embarcados-virtus-cc/optic-power-meter-portable/sfp_8472/a0h.c

/**
 * @file sfp_8472_a0h.c
 * @brief Biblioteca de parsing SFF-8472 – Página A0h (Base ID)
 *
 * @author Alexandre Junior
 * @author Carlos Elias
 * @author Melquisedeque Leite
 * @author Miguel Ryan
 * @author Nicholas Gomes
 * @author Pablo Daniel
 * @author Pedro Lucena
 * @author Pedro Wilson
 *
 * @details
 *  Implementa a leitura e interpretação dos campos da EEPROM A0h
 *  de módulos SFP/SFP+, conforme a especificação SFF-8472.
 */

#include "a0h.h"
#include "defs.h"
#include <stdio.h>
#include <string.h>
#include <stdint.h>

/* ============================================
 * Byte 0 — Identifier
 * ============================================ */
void sfp_parse_a0_base_identifier(const uint8_t *a0_base_data, sfp_a0h_base_t *a0)
{
    if (!a0_base_data || !a0)
        return;

    a0->identifier = (sfp_identifier_t)a0_base_data[A0_IDENTIFIER];
}

/* ============================================
 * Função Getter
 * ============================================ */
sfp_identifier_t sfp_a0_get_identifier(const sfp_a0h_base_t *a0)
{
    if (!a0)
        return SFP_ID_UNKNOWN;

    return a0->identifier;
}

/* ============================================
 * Byte 1 — Extended Identifier
 * ============================================ */
void sfp_parse_a0_base_ext_identifier(const uint8_t *a0_base_data, sfp_a0h_base_t *a0)
{
    if (!a0_base_data || !a0)
        return;

    a0->ext_identifier = a0_base_data[A0_EXT_IDENTIFIER];
}

/* ============================================
 * Função Getter
 * ============================================ */
uint8_t sfp_a0_get_ext_identifier(const sfp_a0h_base_t *a0)
{
    if (!a0)
        return 0x00;

    return a0->ext_identifier;
}

bool sfp_validate_ext_identifier(const sfp_a0h_base_t *a0)
{
    if (!a0)
        return false;

    return (a0->ext_identifier == SFP_EXT_IDENTIFIER_EXPECTED);
}

/* ============================================
 * Byte 2 — Connector
 * ============================================ */
void sfp_parse_a0_base_connector(const uint8_t *a0_base_data, sfp_a0h_base_t *a0)
{
    if (!a0_base_data || !a0)
        return;

    uint8_t connector_raw = a0_base_data[A0_CONNECTOR];
    a0->connector = (sfp_connector_type_t)connector_raw;
}

/* ============================================
 * Função Getter
 * ============================================ */
sfp_connector_type_t sfp_a0_get_connector(const sfp_a0h_base_t *a0)
{
    if (!a0)
        return SFP_CONNECTOR_UNKNOWN;

    return a0->connector;
}

/* ============================================
 * Função de Exposição
 * ============================================ */
const char *sfp_connector_to_string(sfp_connector_type_t connector)
{
    switch (connector) {
        case SFP_CONNECTOR_SC:
            return "SC";
        case SFP_CONNECTOR_FC_STYLE_1:
            return "Fibre Channel Style 1";
        case SFP_CONNECTOR_FC_STYLE_2:
            return "Fibre Channel Style 2";
        case SFP_CONNECTOR_BNC_TNC:
            return "BNC/TNC";
        case SFP_CONNECTOR_FC_COAX:
            return "Fibre Channel Coax";
        case SFP_CONNECTOR_FIBER_JACK:
            return "Fiber Jack";
        case SFP_CONNECTOR_LC:
            return "LC";
        case SFP_CONNECTOR_MT_RJ:
            return "MT-RJ";
        case SFP_CONNECTOR_MU:
            return "MU";
        case SFP_CONNECTOR_SG:
            return "SG";
        case SFP_CONNECTOR_OPTICAL_PIGTAIL:
            return "Optical Pigtail";
        case SFP_CONNECTOR_MPO_1X12:
            return "MPO 1x12";
        case SFP_CONNECTOR_MPO_2X16:
            return "MPO 2x16";
        case SFP_CONNECTOR_HSSDC_II:
            return "HSSDC II";
        case SFP_CONNECTOR_COPPER_PIGTAIL:
            return "Copper Pigtail";
        case SFP_CONNECTOR_RJ45:
            return "RJ45";
        case SFP_CONNECTOR_NO_SEPARABLE:
            return "No Separable Connector";
        default:
            return "Unknown Connector";
    }
}

/* ============================================
 * Bytes 3-10 — Compliance Codes
 * ============================================ */
void sfp_parse_a0_base_compliance(const uint8_t *a0_base_data, sfp_compliance_codes_t *cc)
{
    if (!a0_base_data || !cc)
        return;

    cc->byte3  = a0_base_data[A0_TRANSCEIVER + 0];
    cc->byte4  = a0_base_data[A0_TRANSCEIVER + 1];
    cc->byte5  = a0_base_data[A0_TRANSCEIVER + 2];
    cc->byte6  = a0_base_data[A0_TRANSCEIVER + 3];
    cc->byte7  = a0_base_data[A0_TRANSCEIVER + 4];
    cc->byte8  = a0_base_data[A0_TRANSCEIVER + 5];
    cc->byte9  = a0_base_data[A0_TRANSCEIVER + 6];
    cc->byte10 = a0_base_data[A0_TRANSCEIVER + 7];
}

/* ============================================
 * Decode do Byte 3
 * ============================================ */
static void decode_byte3(const sfp_compliance_codes_t *cc, sfp_compliance_decoded_t *out)
{
    uint8_t b = cc->byte3;
    out->eth_10g_base_er               = (b & (1 << 7)) != 0;
    out->eth_10g_base_lrm              = (b & (1 << 6)) != 0;
    out->eth_10g_base_lr               = (b & (1 << 5)) != 0;
    out->eth_10g_base_sr               = (b & (1 << 4)) != 0;
    out->infiniband_1x_sx              = (b & (1 << 3)) != 0;
    out->infiniband_1x_lx              = (b & (1 << 2)) != 0;
    out->infiniband_1x_copper_active   = (b & (1 << 1)) != 0;
    out->infiniband_1x_copper_passive  = (b & (1 << 0)) != 0;
}

/* ============================================
 * Decode do Byte 4
 * ============================================ */
static void decode_byte4(const sfp_compliance_codes_t *cc, sfp_compliance_decoded_t *out)
{
    uint8_t b = cc->byte4;
    out->escon_mmf  = (b & (1 << 7)) != 0;
    out->escon_smf  = (b & (1 << 6)) != 0;
    out->oc_192_sr  = (b & (1 << 5)) != 0;
    out->sonet_rs_1 = (b & (1 << 4)) != 0;
    out->sonet_rs_2 = (b & (1 << 3)) != 0;
    out->oc_48_lr   = (b & (1 << 2)) != 0;
    out->oc_48_ir   = (b & (1 << 1)) != 0;
    out->oc_48_sr   = (b & (1 << 0)) != 0;
}

/* ============================================
 * Decode do Byte 5
 * ============================================ */
static void decode_byte5(const sfp_compliance_codes_t *cc, sfp_compliance_decoded_t *out)
{
    uint8_t b = cc->byte5;
    out->oc_12_sm_lr = (b & (1 << 6)) != 0;
    out->oc_12_sm_ir = (b & (1 << 5)) != 0;
    out->oc_12_sr    = (b & (1 << 4)) != 0;
    out->oc_3_sm_lr  = (b & (1 << 2)) != 0;
    out->oc_3_sm_ir  = (b & (1 << 1)) != 0;
    out->oc_3_sr     = (b & (1 << 0)) != 0;
}

/* ============================================
 * Decode do Byte 6
 * ============================================ */
static void decode_byte6(const sfp_compliance_codes_t *cc, sfp_compliance_decoded_t *out)
{
    uint8_t b = cc->byte6;
    out->eth_base_px      = (b & (1 << 7)) != 0;
    out->eth_base_bx_10   = (b & (1 << 6)) != 0;
    out->eth_100_base_fx  = (b & (1 << 5)) != 0;
    out->eth_100_base_lx  = (b & (1 << 4)) != 0;
    out->eth_1000_base_t  = (b & (1 << 3)) != 0;
    out->eth_1000_base_cx = (b & (1 << 2)) != 0;
    out->eth_1000_base_lx = (b & (1 << 1)) != 0;
    out->eth_1000_base_sx = (b & (1 << 0)) != 0;
}

/* ============================================
 * Decode do Byte 7
 * ============================================ */
static void decode_byte7(const sfp_compliance_codes_t *cc, sfp_compliance_decoded_t *out)
{
    uint8_t b = cc->byte7;
    out->fc_very_long_distance      = (b & (1 << 7)) != 0;
    out->fc_short_distance          = (b & (1 << 6)) != 0;
    out->fc_intermediate_distance   = (b & (1 << 5)) != 0;
    out->fc_long_distance           = (b & (1 << 4)) != 0;
    out->fc_medium_distance         = (b & (1 << 3)) != 0;
    out->shortwave_laser_sa         = (b & (1 << 2)) != 0;
    out->longwave_laser_lc          = (b & (1 << 1)) != 0;
    out->electrical_inter_enclosure = (b & (1 << 0)) != 0;
}

/* ============================================
 * Decode do Byte 8
 * ============================================ */
static void decode_byte8(const sfp_compliance_codes_t *cc, sfp_compliance_decoded_t *out)
{
    uint8_t b = cc->byte8;
    out->electrical_intra_enclosure = (b & (1 << 7)) != 0;
    out->shortwave_laser_sn         = (b & (1 << 6)) != 0;
    out->shortwave_laser_sl        = (b & (1 << 5)) != 0;
    out->longwave_laser_ll          = (b & (1 << 4)) != 0;
    out->active_cable               = (b & (1 << 3)) != 0;
    out->passive_cable              = (b & (1 << 2)) != 0;
}

/* ============================================
 * Decode do Byte 9
 * ============================================ */
static void decode_byte9(const sfp_compliance_codes_t *cc, sfp_compliance_decoded_t *out)
{
    uint8_t b = cc->byte9;
    out->twin_axial_pair = (b & (1 << 7)) != 0;
    out->twisted_pair    = (b & (1 << 6)) != 0;
    out->miniature_coax  = (b & (1 << 5)) != 0;
    out->video_coax      = (b & (1 << 4)) != 0;
    out->multimode_m6    = (b & (1 << 3)) != 0;
    out->multimode_m5    = (b & (1 << 2)) != 0;
    out->single_mode     = (b & (1 << 0)) != 0;
}

/* ============================================
 * Decode do Byte 10
 * ============================================ */
static void decode_byte10(const sfp_compliance_codes_t *cc, sfp_compliance_decoded_t *out)
{
    uint8_t b = cc->byte10;
    out->cs_1200_mbps = (b & (1 << 7)) != 0;
    out->cs_800_mbps  = (b & (1 << 6)) != 0;
    out->cs_1600_mbps = (b & (1 << 5)) != 0;
    out->cs_400_mbps  = (b & (1 << 4)) != 0;
    out->cs_3200_mbps = (b & (1 << 3)) != 0;
    out->cs_200_mbps  = (b & (1 << 2)) != 0;
    out->see_byte_62  = (b & (1 << 1)) != 0;
    out->cs_100_mbps  = (b & (1 << 0)) != 0;
}

/* ============================================
 * Função principal para decodificação de todos os bytes
 * ============================================ */
void sfp_a0_decode_compliance(const sfp_compliance_codes_t *cc, sfp_compliance_decoded_t *out)
{
    if (!cc || !out)
        return;

    memset(out, 0, sizeof(*out));
    decode_byte3(cc, out);
    decode_byte4(cc, out);
    decode_byte5(cc, out);
    decode_byte6(cc, out);
    decode_byte7(cc, out);
    decode_byte8(cc, out);
    decode_byte9(cc, out);
    decode_byte10(cc, out);
}

/* ============================================
 * Função de Exposição
 * ============================================ */
void sfp_a0_print_compliance(const sfp_compliance_decoded_t *c)
{
    if (!c) return;

    /* ==============================
     * Byte 3 — Ethernet / InfiniBand
     * ============================== */
    printf("\n[Byte 3] Ethernet / InfiniBand:\n");

    if (c->eth_10g_base_er)  printf("  - 10GBASE-ER\n");
    if (c->eth_10g_base_lrm) printf("  - 10GBASE-LRM\n");
    if (c->eth_10g_base_lr)  printf("  - 10GBASE-LR\n");
    if (c->eth_10g_base_sr)  printf("  - 10GBASE-SR\n");

    if (c->infiniband_1x_sx)             printf("  - InfiniBand 1X SX\n");
    if (c->infiniband_1x_lx)             printf("  - InfiniBand 1X LX\n");
    if (c->infiniband_1x_copper_active)  printf("  - InfiniBand 1X Copper Active\n");
    if (c->infiniband_1x_copper_passive) printf("  - InfiniBand 1X Copper Passive\n");

    /* ======================
     * Byte 4 — ESCON / SONET
     * ====================== */
    printf("\n[Byte 4] ESCON / SONET:\n");

    if (c->escon_mmf)   printf("  - ESCON MMF\n");
    if (c->escon_smf)   printf("  - ESCON SMF\n");
    if (c->oc_192_sr)   printf("  - OC-192 SR\n");
    if (c->sonet_rs_1)  printf("  - SONET RS-1\n");
    if (c->sonet_rs_2)  printf("  - SONET RS-2\n");
    if (c->oc_48_lr)    printf("  - OC-48 LR\n");
    if (c->oc_48_ir)    printf("  - OC-48 IR\n");
    if (c->oc_48_sr)    printf("  - OC-48 SR\n");

    /* ======================
     * Byte 5 — SONET
     * ====================== */
    printf("\n[Byte 5] SONET:\n");

    if (c->oc_12_sm_lr) printf("  - OC-12 SM LR\n");
    if (c->oc_12_sm_ir) printf("  - OC-12 SM IR\n");
    if (c->oc_12_sr)    printf("  - OC-12 SR\n");
    if (c->oc_3_sm_lr)  printf("  - OC-3 SM LR\n");
    if (c->oc_3_sm_ir)  printf("  - OC-3 SM IR\n");
    if (c->oc_3_sr)     printf("  - OC-3 SR\n");

    /* ======================
     * Byte 6 — Ethernet
     * ====================== */
    printf("\n[Byte 6] Ethernet:\n");

    if (c->eth_base_px)      printf("  - BASE-PX\n");
    if (c->eth_base_bx_10)   printf("  - BASE-BX10\n");
    if (c->eth_100_base_fx)  printf("  - 100BASE-FX\n");
    if (c->eth_100_base_lx)  printf("  - 100BASE-LX\n");
    if (c->eth_1000_base_t)  printf("  - 1000BASE-T\n");
    if (c->eth_1000_base_cx) printf("  - 1000BASE-CX\n");
    if (c->eth_1000_base_lx) printf("  - 1000BASE-LX\n");
    if (c->eth_1000_base_sx) printf("  - 1000BASE-SX\n");

    /* ====================================
     * Byte 7 — FC Link Length & Technology
     * ==================================== */
    printf("\n[Byte 7] Fibre Channel — Link Length / Technology:\n");

    if (c->fc_very_long_distance)      printf("  - Very Long Distance\n");
    if (c->fc_short_distance)          printf("  - Short Distance\n");
    if (c->fc_intermediate_distance)   printf("  - Intermediate Distance\n");
    if (c->fc_long_distance)           printf("  - Long Distance\n");
    if (c->fc_medium_distance)         printf("  - Medium Distance\n");
    if (c->shortwave_laser_sa)          printf("  - Shortwave Laser (SA)\n");
    if (c->longwave_laser_lc)           printf("  - Longwave Laser (LC)\n");
    if (c->electrical_inter_enclosure)  printf("  - Electrical Inter-Enclosure\n");

    /* ==============================================
     * Byte 8 — FC & SFP+ Cable Technology
     * ============================================== */
    printf("\n[Byte 8] Fibre Channel / Cable Technology:\n");

    if (c->electrical_intra_enclosure) printf("  - Electrical Intra-Enclosure\n");
    if (c->shortwave_laser_sn)         printf("  - Shortwave Laser (SN)\n");
    if (c->shortwave_laser_sl)         printf("  - Shortwave Laser (SL)\n");
    if (c->longwave_laser_ll)          printf("  - Longwave Laser (LL)\n");
    if (c->active_cable)               printf("  - Active SFP+ Cable\n");
    if (c->passive_cable)              printf("  - Passive SFP+ Cable\n");

    /* ==============================
     * Byte 9 — FC Transmission Media
     * ============================== */
    printf("\n[Byte 9] Fibre Channel — Transmission Media:\n");

    if (c->twin_axial_pair) printf("  - Twin Axial Pair\n");
    if (c->twisted_pair)    printf("  - Twisted Pair\n");
    if (c->miniature_coax)  printf("  - Miniature Coax\n");
    if (c->video_coax)      printf("  - Video Coax\n");
    if (c->multimode_m6)    printf("  - Multimode 62.5 µm\n");
    if (c->multimode_m5)    printf("  - Multimode 50 µm\n");
    if (c->single_mode)     printf("  - Single Mode\n");

    /* ==============================
     * Byte 10 — FC Channel Speed
     * ============================== */
    printf("\n[Byte 10] Fibre Channel — Speed:\n");

    if (c->cs_1200_mbps) printf("  - 1200 Mbps\n");
    if (c->cs_800_mbps)  printf("  - 800 Mbps\n");
    if (c->cs_1600_mbps) printf("  - 1600 Mbps\n");
    if (c->cs_400_mbps)  printf("  - 400 Mbps\n");
    if (c->cs_3200_mbps) printf("  - 3200 Mbps\n");
    if (c->cs_200_mbps)  printf("  - 200 Mbps\n");
    if (c->cs_100_mbps)  printf("  - 100 Mbps\n");
}

/* =========================================================
 * Byte 8 — Natureza física do meio
 * =========================================================*/
static bool sfp_is_copper(uint8_t byte8)
{
    return ((byte8 & (1 << 2)) != 0) || ((byte8 & (1 << 3)) != 0);
}

/* ============================================
 * Byte 11 — Encoding
 * ============================================ */
void sfp_parse_a0_base_encoding(const uint8_t *a0_base_data, sfp_a0h_base_t *a0)
{
    if (!a0_base_data || !a0)
        return;
    a0->encoding = (sfp_encoding_codes_t)a0_base_data[A0_ENCODING];
}

/* ============================================
 * Função Getter
 * ============================================ */
sfp_encoding_codes_t sfp_a0_get_encoding(const sfp_a0h_base_t *a0)
{
    if (!a0)
        return SFP_ENC_UNSPECIFIED;
    return a0->encoding;
}

/* ============================================
 * Função de Exposição
 * ============================================ */
void sfp_print_encoding(sfp_encoding_codes_t encoding)
{
    printf("\n[Byte 11] Encoding:\n");

    switch ((uint8_t)encoding) {
        case SFP_ENC_UNSPECIFIED:
            printf("  - Unspecified\n");
            break;
        case SFP_ENC_8B_10B:
            printf("  - 8B/10B\n");
            break;
        case SFP_ENC_4B_5B:
            printf("  - 4B/5B\n");
            break;
        case SFP_ENC_NRZ:
            printf("  - NRZ\n");
            break;
        case SFP_ENC_MANCHESTER:
            printf("  - Manchester\n");
            break;
        case SFP_ENC_SONET_SCRAMBLED:
            printf("  - SONET Scrambled\n");
            break;
        case SFP_ENC_64B_66B:
            printf("  - 64B/66B\n");
            break;
        case SFP_ENC_256B_257B:
            printf("  - 256B/257B\n");
            break;
        case SFP_ENC_PAM4:
            printf("  - PAM4\n");
            break;
        default:
            printf("  - Reserved / Unknown Code (0x%02X)\n", (uint8_t)encoding);
            break;
    }
}

/* ============================================
 * Byte 12 — Signaling Rate, Nominal
 * ============================================ */
void sfp_parse_a0_base_nominal_rate(const uint8_t *a0_base_data, sfp_a0h_base_t *a0)
{
    if (!a0_base_data || !a0)
        return;

    /* Byte 12 — Signaling Rate, Nominal (somente leitura crua do bloco base) */
    uint8_t raw = a0_base_data[SFP_A0_BYTE_NOMINAL_RATE];
    if (raw == SFP_NOMINAL_RATE_RAW_UNSPECIFIED) {
        a0->nominal_rate_status = SFP_NOMINAL_RATE_NOT_SPECIFIED;
        a0->nominal_rate = 0;
    } else if (raw == SFP_NOMINAL_RATE_RAW_EXTENDED) {
        a0->nominal_rate_status = SFP_NOMINAL_RATE_EXTENDED;
        a0->nominal_rate = 25400;
    } else {
        a0->nominal_rate_status = SFP_NOMINAL_RATE_VALID;
        a0->nominal_rate = (uint32_t)raw * 100;
    }
}

/* ============================================
 * Método Getter
 * ============================================ */
uint8_t sfp_a0_get_nominal_rate_mbd(const sfp_a0h_base_t *a0, sfp_nominal_rate_status_t *status)
{
    if (!a0) {
        if (status)
            *status = SFP_NOMINAL_RATE_NOT_SPECIFIED;
        return 0;
    }

    if (status)
        *status = a0->nominal_rate_status;
    return a0->nominal_rate;
}

/* ============================================
 * Byte 13 — Rate Identifier
 * ============================================ */
void sfp_parse_a0_base_rate_identifier(const uint8_t *a0_base_date, sfp_a0h_base_t *a0)
{
    if (!a0_base_date || !a0)
        return;

    a0->rate_identifier = (sfp_rate_select) a0_base_date[A0_RATE_IDENTIFIER];
}

/* ============================================
 * Método Getter
 * ============================================ */
sfp_rate_select sfp_a0_get_rate_identifier(const sfp_a0h_base_t *a0)
{
    if (!a0)
        return 0;

    return a0->rate_identifier;
}

/* =========================================================
 * Byte 14 — Length (SMF) or Attenuation (Copper)
 *
 * @details
 *  - Para fibra SMF: Representa o alcance em quilômetros (km)
 *    Unidade: 1 km (valor 0x01 = 1 km, 0x64 = 100 km)
 *
 *  - Para cabo de cobre: Representa a atenuação em dB/100m
 *    Unidade: 0.5 dB/100m (valor 0x01 = 0.5 dB/100m)
 *
 *  - Valores especiais:
 *    0x00: Não suportado ou informação não disponível
 *    0xFF: Valor superior ao máximo representável (> 254 km ou > 127 dB/100m)
 * =========================================================*/

void sfp_parse_a0_base_smf_km(const uint8_t *a0_base_data, sfp_a0h_base_t *a0)
{
    if (!a0_base_data || !a0)
        return;

    uint8_t raw = a0_base_data[A0_LENGTH_SMF_KM];

    uint8_t byte8 = a0_base_data[A0_TRANSCEIVER + 5];

    bool is_copper = sfp_is_copper(byte8);

    /*
     * Fluxo Principal + Secundários
     */
    if (raw == 0x00) {
        /*
         * Fluxo Secundário 2 (caso 00h):
         * Não há informação explícita de alcance SMF ou atenuação de cobre.
         */
        a0->smf_status_km   = SFP_SMF_LEN_NOT_SUPPORTED;
        a0->smf_length_km = 0;
    }
    else if (raw == 0xFF) {
        /*
         * Fluxo Secundário (caso FFh):
         * Comprimento/Atenuação superior ao máximo nominal representável.
         *
         * - Fibra SMF: alcance > 254 km
         * - Cabo de cobre: atenuação > 127 dB/100m
         *
         * O valor armazenado representa o limite inferior/superior conhecido.
         */
        a0->smf_status_km   = SFP_SMF_LEN_EXTENDED;

        if (is_copper)
            a0->smf_length_km = 254; /* 254 * 0.5 = 127 dB/100m */
        else
            a0->smf_length_km = 254; /* 254 km */
    }
    else {
        /*
         * Fluxo Principal:
         * Valor válido (01h–FEh)
         *
         * - Fibra SMF: unidade de 1 km (valor direto)
         * - Cabo de cobre: unidade de 0.5 dB/100m (valor * 0.5)
         */
        a0->smf_status_km   = SFP_SMF_LEN_VALID;
        a0->smf_length_km = (uint16_t)raw;
    }
}

/* ============================================
 * Função Getter
 * ============================================ */
uint16_t sfp_a0_get_smf_length_km(const sfp_a0h_base_t *a0, sfp_smf_length_status_t *status)
{
    if (!a0) {
        if (status)
            *status = SFP_SMF_LEN_NOT_SUPPORTED;
        return 0;
    }
    if (status)
        *status = a0->smf_status_km;
    return a0->smf_length_km;
}


/* =========================================================
 * Byte 15 — Length (SMF) or Attenuation (Copper) (Units 100m)
 * =========================================================*/
void sfp_parse_a0_base_smf_m(const uint8_t *a0_base_data, sfp_a0h_base_t *a0)
{
    if (!a0_base_data || !a0)
        return;

    uint8_t raw = a0_base_data[A0_LENGTH_SMF_100M];

    uint8_t byte8 = a0_base_data[A0_TRANSCEIVER + 5];

    bool is_copper = sfp_is_copper(byte8);

    if (raw == 0x00) {
        a0->smf_status_m = SFP_SMF_LEN_NOT_SUPPORTED;
        a0->smf_length_m = 0;
    }
    else if (raw == 0xFF) {
        a0->smf_status_m = SFP_SMF_LEN_EXTENDED;

        a0->smf_length_m = 2540;
    }
    else {
        if (is_copper)
            a0->smf_length_m = raw;
        else
            a0->smf_length_m = raw * 100;
        a0->smf_status_m = SFP_SMF_LEN_VALID;
    }
}

/* ============================================
 * Função Getter
 * ============================================ */
uint16_t sfp_a0_get_smf_length_m(const sfp_a0h_base_t *a0, sfp_smf_length_status_t *status)
{
    if (!a0) {
        if (status)
            *status = SFP_SMF_LEN_NOT_SUPPORTED;
        return 0;
    }
    if (status)
        *status = a0->smf_status_m;
    return a0->smf_length_m;
}

/* ============================================
 * Byte 16 — OM2 Length (50 µm)
 * ============================================ */
void sfp_parse_a0_base_om2(const uint8_t *a0_base_data, sfp_a0h_base_t *a0)
{
    if (!a0_base_data || !a0)
        return;

    uint8_t raw = a0_base_data[A0_LENGTH_OM2_10M];

    /*
     * Fluxo Principal + Secundários
     */
    if (raw == 0x00) {
        /*
         * Fluxo Secundário 2 (caso 00h):
         * Não suportado ou deve ser determinado por outros meios.
         */
        a0->om2_status   = SFP_OM2_LEN_NOT_SUPPORTED;
        a0->om2_length_m = 0;
    }
    else if (raw == 0xFF) {
        /*
         * Fluxo Secundário 2 (caso FFh):
         * Alcance > 2.54 km.
         */
        a0->om2_status   = SFP_OM2_LEN_EXTENDED;
        a0->om2_length_m = 2540; /* Limite inferior conhecido (254 * 10) */
    }
    else {
        /*
         * Fluxo Principal:
         * Valor válido (01h–FEh)
         * Unidade: 10 metros
         */
        a0->om2_status   = SFP_OM2_LEN_VALID;
        a0->om2_length_m = (uint16_t)raw * 10;
    }
}

/* ============================================
 * Função Getter
 * ============================================ */
uint16_t sfp_a0_get_om2_length_m(const sfp_a0h_base_t *a0, sfp_om2_length_status_t *status)
{
    if (!a0) {
        if (status)
            *status = SFP_OM2_LEN_NOT_SUPPORTED;
        return 0;
    }
    if (status)
        *status = a0->om2_status;
    return a0->om2_length_m;
}

/* ============================================
 * Byte 17 — OM1 Length (62.5 µm)
 * ============================================ */
void sfp_parse_a0_base_om1(const uint8_t *a0_base_data, sfp_a0h_base_t *a0)
{
    if (!a0_base_data || !a0)
        return;

    uint8_t raw = a0_base_data[A0_LENGTH_OM1_10M];

    /*
     * Fluxo Principal + Secundários
     */
    if (raw == 0x00) {
        /*
         * Fluxo Secundário 2 (caso 00h):
         * Não há informação explícita de alcance OM1.
         * Inferência futura via bytes 3–10.
         */
        a0->om1_status   = SFP_OM1_LEN_NOT_SUPPORTED;
        a0->om1_length_m = 0;
    }
    else if (raw == 0xFF) {
        /*
         * Fluxo Secundário 2 (caso FFh):
         * Alcance superior ao máximo nominal do campo.
         * Representa > 2,54 km.
         */
        a0->om1_status   = SFP_OM1_LEN_EXTENDED;
        a0->om1_length_m = 2540; /* Limite inferior conhecido */
    }
    else {
        /*
         * Fluxo Principal / Secundário 1:
         * Valor válido (01h–FEh)
         * Unidade: 10 metros
         */
        a0->om1_status   = SFP_OM1_LEN_VALID;
        a0->om1_length_m = (uint16_t)raw * 10;
    }
}

/* ============================================
 * Função Getter
 * ============================================ */
uint16_t sfp_a0_get_om1_length_m(const sfp_a0h_base_t *a0, sfp_om1_length_status_t *status)
{
    if (!a0) {
        if (status)
            *status = SFP_OM1_LEN_NOT_SUPPORTED;
        return 0;
    }
    if (status)
        *status = a0->om1_status;
    return a0->om1_length_m;
}

/* ============================================
 * Byte 18 — OM4 or Copper Cable Length
 * ============================================ */
void sfp_parse_a0_base_om4_or_copper(const uint8_t *a0_base_data, sfp_a0h_base_t *a0)
{
    if (!a0_base_data || !a0)
        return;

    uint8_t raw_length = a0_base_data[A0_LENGTH_OM4_10M];

    uint8_t byte8 = a0_base_data[A0_TRANSCEIVER + 5];

    bool is_copper = sfp_is_copper(byte8);

    /*
     * Fluxo Principal + Secundários
     */
    if (raw_length == 0x00) {
        /*
         * Fluxo Secundário 2 (caso 00h):
         * Não há informação explícita de comprimento de OM4 ou o cobre sem informação válida.
         */
        a0->om4_or_copper_status = SFP_OM4_LEN_NOT_SUPPORTED;
        a0->om4_or_copper_length_m = 0;
    }
    else if (raw_length == 0xFF) {
        /*
         * Fluxo Secundário (caso FFh):
         * Comprimento superior ao máximo nominal representável
         * pelo campo.
         *
         * - Cabo de cobre: comprimento > 254 m
         * - OM4: comprimento > 2,54 km
         *
         * O valor armazenado representa o limite inferior conhecido.
         */
        a0->om4_or_copper_status = SFP_OM4_LEN_EXTENDED;

        if (is_copper)
            a0->om4_or_copper_length_m = 254;
        else
            a0->om4_or_copper_length_m = 2540;
    }
    else {
        /*
         * Fluxo Principal:
         * Valor válido (01h–FEh)
         *
         * - OM4: unidades de 10 metros
         * - Cabo de cobre: unidades de 1 metro
         */
        a0->om4_or_copper_status = SFP_OM4_LEN_VALID;

        if (is_copper)
            a0->om4_or_copper_length_m = raw_length;
        else
            a0->om4_or_copper_length_m = (uint16_t)raw_length * 10;
    }
}

/* ============================================
 * Função Getter
 * ============================================ */
uint16_t sfp_a0_get_om4_copper_or_length_m(const sfp_a0h_base_t *a0, sfp_om4_length_status_t *status)
{
    if (!a0) {
        if (status)
            *status = SFP_OM4_LEN_NOT_SUPPORTED;
        return 0;
    }
    if (status)
        *status = a0->om4_or_copper_status;
    return a0->om4_or_copper_length_m;
}

/* ============================================
 * Byte 19 — OM3 or Optical/Cable Physical Interconnect Length
 * ============================================ */
void sfp_parse_a0_base_om3_or_cable(const uint8_t *a0_base_data, sfp_a0h_base_t *a0)
{
    if (!a0_base_data || !a0)
        return;

    uint8_t raw = a0_base_data[A0_LENGTH_OM3_10M];
    uint8_t byte8 = a0_base_data[A0_TRANSCEIVER + 5];
    bool is_copper = sfp_is_copper(byte8);

    if (!is_copper) {
        if (raw == 0x00) {
            a0->om3_or_cable_status = SFP_OM3_LEN_NOT_SUPPORTED;
            a0->om3_or_cable_length_m = 0;
        } else if (raw == 0xFF) {
            a0->om3_or_cable_status = SFP_OM3_LEN_EXTENDED;
            a0->om3_or_cable_length_m = 2540;
        } else {
            a0->om3_or_cable_status = SFP_OM3_LEN_VALID;
            a0->om3_or_cable_length_m = raw * 10;
        }
    } else {
        uint8_t multiplier_bits = (raw >> 6) & 0x03;
        uint8_t base_length = raw & 0x3F;
        float multiplier = 1.0f;

        switch (multiplier_bits) {
            case 0: multiplier = 0.1f;  break;
            case 1: multiplier = 1.0f;  break;
            case 2: multiplier = 10.0f; break;
            case 3: multiplier = 100.0f; break;
        }

        a0->om3_or_cable_status = SFP_OM3_LEN_VALID;
        a0->om3_or_cable_length_m = base_length * multiplier;
    }
}

/* ============================================
 * Função Getter
 * ============================================ */
uint32_t sfp_a0_get_om3_cable_length_m(const sfp_a0h_base_t *a0, sfp_om3_length_status_t *status)
{
    if (!a0) {
        if (status)
            *status = SFP_OM3_LEN_NOT_SUPPORTED;
        return 0;
    }
    if (status)
        *status = a0->om3_or_cable_status;
    return a0->om3_or_cable_length_m;
}


/* ============================================
 * Bytes 20-35 — Vendor Name
 * ============================================ */

/* ASCII imprimível padrão (inclui espaço) */
static bool sfp_is_printable_ascii(uint8_t c)
{
    return (c >= 0x20u) && (c <= 0x7Eu);
}

static bool sfp_a0_vendor_name_is_valid(const sfp_a0h_base_t *a0)
{
    if (!a0)
        return false;

    bool found_padding = false;
    bool has_content = false;

    /* Todos os bytes devem ser ASCII imprimível */
    for (size_t i = 0; i < SFP_A0_LEN_VENDOR_NAME; i++) {
        uint8_t c = (uint8_t)a0->vendor_name[i];
        if (!sfp_is_printable_ascii(c))
            return false;

        if (c == 0x20u) {
            found_padding = true;
            continue;
        }

        if (found_padding)
            return false;

        has_content = true;
    }

    /* Não pode ser vazio (todos espaços) */
    return has_content;
}

void sfp_parse_a0_base_vendor_name(const uint8_t *a0_base_data, sfp_a0h_base_t *a0)
{
    if (!a0_base_data || !a0)
        return;

    /* Vendor Name (16 bytes) - ASCII, alinhado a esquerda, padding com 0x20 */
    memcpy(a0->vendor_name, &a0_base_data[SFP_A0_BYTE_VENDOR_NAME], SFP_A0_LEN_VENDOR_NAME);
    a0->is_valid_vendor_name = sfp_a0_vendor_name_is_valid(a0);
}

/* ============================================
 * Método Getter
 * ============================================ */
const char *sfp_a0_get_vendor_name(const sfp_a0h_base_t *a0)
{
    if (!a0 || !a0->is_valid_vendor_name)
        return "Invalid";

    return a0->vendor_name;
}

/* ============================================
 * Byte 36 — Extended Compliance Codes (SFF-8024 Table 4-4)
 * ============================================ */
void sfp_parse_a0_base_ext_compliance(const uint8_t *a0_base_data, sfp_a0h_base_t *a0)
{
    if (!a0_base_data || !a0)
        return;
    a0->ext_compliance = (sfp_extended_spec_compliance_code_t)a0_base_data[A0_EXT_TRANSCEIVER];
}

/* ============================================
 * Função Getter
 * ============================================ */
sfp_extended_spec_compliance_code_t sfp_a0_get_ext_compliance(const sfp_a0h_base_t *a0)
{
    if (!a0)
        return EXT_SPEC_COMPLIANCE_UNSPECIFIED;
    return a0->ext_compliance;
}

/* ============================================
 * Byte 37-39 — Vendor OUI
 * ============================================ */
void sfp_parse_a0_base_vendor_oui(const uint8_t *a0_base_data,
                                  sfp_a0h_base_t *a0)
{
    if (!a0_base_data || !a0)
        return;

    /* Bytes 37–39: Vendor OUI (IEEE Company Identifier) */
    a0->vendor_oui[0] = a0_base_data[A0_VENDOR_OUI + 0];
    a0->vendor_oui[1] = a0_base_data[A0_VENDOR_OUI + 1];
    a0->vendor_oui[2] = a0_base_data[A0_VENDOR_OUI + 2];
}

/* ============================================
 * Função Getter
 * ============================================ */
bool sfp_a0_get_vendor_oui(const sfp_a0h_base_t *a0,
                           uint8_t oui_buffer[3])
{
    if (!a0 || !oui_buffer)
        return false;

    oui_buffer[0] = a0->vendor_oui[0];
    oui_buffer[1] = a0->vendor_oui[1];
    oui_buffer[2] = a0->vendor_oui[2];

    return true;
}

/* ============================================
*    Converte o Vendor OUI para um identificador de 24 bits.
*    @param a0 Ponteiro para a estrutura sfp_a0h_base_t contendo o Vendor OUI já parseado.
*    @return Valor inteiro de 24 bits representando o Vendor OUI. Caso a estrutura seja inválida, retorna 0.
* ============================================ */
uint32_t sfp_vendor_oui_to_u32(const sfp_a0h_base_t *a0)
{
    if (!a0)
        return 0;

    return ((uint32_t)a0->vendor_oui[0] << 16) |
           ((uint32_t)a0->vendor_oui[1] << 8)  |
           ((uint32_t)a0->vendor_oui[2]);
}

/* ============================================
 * Byte 40-55 — Vendor PN (Part Number)
 * ============================================ */
void sfp_parse_a0_base_vendor_pn(const uint8_t *a0_base_data, sfp_a0h_base_t *a0)
{
    if (!a0_base_data || !a0)
        return;

    memcpy (a0->vendor_pn, &a0_base_data[A0_VENDOR_PN], 16);
}

const char *sfp_a0_get_vendor_pn(const sfp_a0h_base_t *a0)
{
    if (!a0) {
        return "Invalid";
    }

    return a0->vendor_pn;
}


/* ============================================
 * Byte 56-59 — Vendor Rev
 * ============================================ */
void sfp_parse_a0_base_vendor_rev(const uint8_t *a0_base_data, sfp_a0h_base_t *a0)
{
    if (!a0_base_data || !a0)
        return;

    memcpy (a0->vendor_rev, &a0_base_data[A0_VENDOR_REV], 4);
    a0->vendor_rev[4] = '\0';
}

const char *sfp_a0_get_vendor_rev(const sfp_a0h_base_t *a0)
{
    if (!a0) {
        return "Invalid";
    }

    return a0->vendor_rev;
}


/* ============================================
 * Byte 60-61 — Wavelength
 * ============================================ */
static sfp_variant_t sfp_detect_variant(uint8_t byte8)
{
    bool passive = (byte8 & (1 << 2)) != 0;
    bool active  = (byte8 & (1 << 3)) != 0;

    if (active)  return SFP_VARIANT_ACTIVE_CABLE;
    if (passive) return SFP_VARIANT_PASSIVE_CABLE;
    return SFP_VARIANT_OPTICAL;
}

void sfp_parse_a0_base_media(const uint8_t *a0_base_data, sfp_a0h_base_t *a0)
{
    if (!a0_base_data || !a0)
        return;

    uint8_t byte8  = a0_base_data[A0_TRANSCEIVER + 5];
    uint8_t byte60 = a0_base_data[A0_WAVELENGTH];
    uint8_t byte61 = a0_base_data[A0_WAVELENGTH + 1];

    a0->variant = sfp_detect_variant(byte8);

    if (a0->variant == SFP_VARIANT_OPTICAL) {
        a0->wavelength_nm = ((uint16_t)byte60 << 8) | byte61;
    } else if (a0->variant == SFP_VARIANT_PASSIVE_CABLE || a0->variant == SFP_VARIANT_ACTIVE_CABLE) {
       a0->cable_compliance = byte60;
   }

}

sfp_variant_t sfp_a0_get_variant(const sfp_a0h_base_t *a0)
{
    if (!a0) return SFP_VARIANT_UNKNOWN;
    return a0->variant;
}

bool sfp_a0_get_wavelength_nm(const sfp_a0h_base_t *a0, uint16_t *nm)
{
    if (!a0 || !nm)
        return false;

    if (a0->variant != SFP_VARIANT_OPTICAL)
        return false;

    *nm = a0->wavelength_nm;
    return true;
}

bool sfp_a0_get_cable_compliance(const sfp_a0h_base_t *a0, uint8_t *bits)
{
    if (!a0 || !bits)
        return false;

    if (a0->variant != SFP_VARIANT_PASSIVE_CABLE && a0->variant != SFP_VARIANT_ACTIVE_CABLE)
        return false;

    *bits = a0->cable_compliance;
    return true;
}

/* ============================================
 * Byte 62 — Fibre Channel Speed 2
 * ============================================ */
void sfp_parse_a0_fc_speed_2(const uint8_t *a0_base_data, sfp_a0h_base_t *a0)
{
    if (!a0_base_data || !a0)
        return;

    a0->fc_speed2 = a0_base_data[A0_FIBRE_CHANNEL_SPD2];
}

/* ============================================
 * Função Getter
 * ============================================ */
bool sfp_get_a0_fc_speed_2(const sfp_a0h_base_t *a0, const sfp_compliance_decoded_t *comp)
{
    uint8_t b = a0->fc_speed2;

    if (!a0 || !comp)
        return false;

    if (!comp->see_byte_62) {
        return false;
    }

    uint8_t speed = b & (1 << 0);

    return speed;
}

/* ============================================
 * Byte 63 — CC_BASE Checksum
 * ============================================ */
void sfp_parse_a0_base_cc_base(const uint8_t *a0_base_data, sfp_a0h_base_t *a0)
{
    if (!a0_base_data || !a0)
        return;

    uint16_t sum = 0;
    for (int i = 0; i < 63; i++) {
        sum += a0_base_data[i];
    }

    uint8_t sum_mod256 = (uint8_t)(sum & 0xFF);

    uint8_t checksum_byte = a0_base_data[A0_CC_BASE];

    a0->cc_base_is_valid = (sum_mod256 == checksum_byte);

    a0->cc_base = checksum_byte;
}

/* ============================================
 * Função Getter
 * ============================================ */
bool sfp_a0_get_cc_base_is_valid(const sfp_a0h_base_t *a0)
{
    if (!a0)
        return false;
    return a0->cc_base_is_valid;
}
/* ============================================
 * EXTEND FIELDS A0H
 * ============================================ */

/* ============================================
 * Byte 92 — DMI IMPLEMENTED
 * ============================================ */

void sfp_parse_a0_extended_dmi(const uint8_t *a0_data,sfp_a0h_extended_t *a0) {
    if (!a0_data || !a0) return;

    // Obtém o byte de Tipo de Monitoramento de Diagnóstico (Byte 92 do A0h)
    uint8_t diag_type = a0_data[A0_DIAG_MONITORING_TYPE];

    // Conforme a Tabela 8-5, o Bit 6 indica se o monitoramento digital (A2h)
    // está implementado no transceptor.
    bool dmi_implemented = (diag_type & (1 << SFP_A0_BIT_DMI_IMPL));

    a0->dmi_implemented = dmi_implemented;
}

/* ============================================
 * Função Getter
 * ============================================ */

bool sfp_a0_get_dmi(const sfp_a0h_extended_t *a0)
{
  if(!a0)
    return false;
  return a0->dmi_implemented;
}

/* ============================================
 * Byte 92 — Change Address required
 * ============================================ */

void sfp_parse_a0_extended_change_addr_req(const uint8_t *a0_data,sfp_a0h_extended_t *a0){
  if(!a0_data || !a0) return;

  uint8_t byte92 = a0_data[A0_DIAG_MONITORING_TYPE];

  bool change_addr_req = (byte92 & (1 << SFP_A0_BIT_ADDR_CHANGE_REQ));

  a0->change_addr_req = change_addr_req;
}

/* ============================================
 * Função Getter
 * ============================================ */

bool sfp_a0_get_change_addr_req(const sfp_a0h_extended_t *a0){
  if(!a0) return false;

  return a0->change_addr_req;
}

/* ============================================
 * Byte 92 — Calibration
 * ============================================ */

void sfp_parse_a0_extended_calibration(const uint8_t *a0_data,sfp_a0h_extended_t *a0){

  if(!a0_data || !a0) return;

  uint8_t byte92 = a0_data[A0_DIAG_MONITORING_TYPE];

  if (byte92 & (1 << SFP_A0_BIT_INTERNAL_CAL)) {
        a0->calibration = SFP_CAL_INTERNAL;
  }else if(byte92 & (1 << SFP_A0_BIT_EXTERNAL_CAL)){
        a0->calibration = SFP_CAL_EXTERNAL;
  }
  else{
    a0->calibration = SFP_CAL_NOT_SUPPORTED;
  }
}

/* ============================================
 * Função Getter
 * ============================================ */

sfp_cal_type_t sfp_a0_get_calibration(const sfp_a0h_extended_t *a0){
  if(!a0) return SFP_CAL_NOT_SUPPORTED;

  return a0->calibration;
}
